jluisalegria/Access_Control/Firmware/Access_Control_IoT_Contest/figures/1import.png

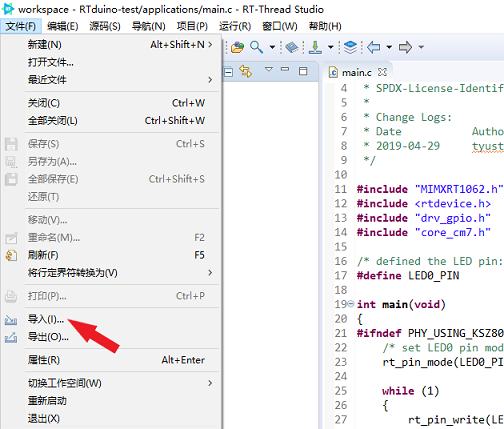
Firmware/Access_Control_IoT_Contest/figures/1import.png
