jluisalegria/Access_Control/Firmware/Access_Control_IoT_Contest/figures/2workspace.png

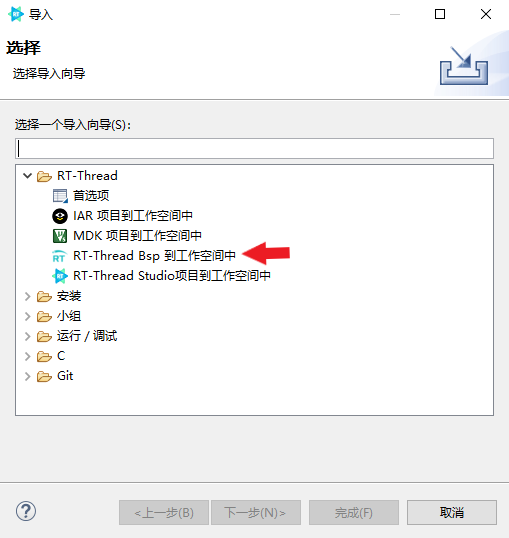
Firmware/Access_Control_IoT_Contest/figures/2workspace.png
