jluisalegria/Access_Control/Firmware/Access_Control_IoT_Contest/figures/3info.png

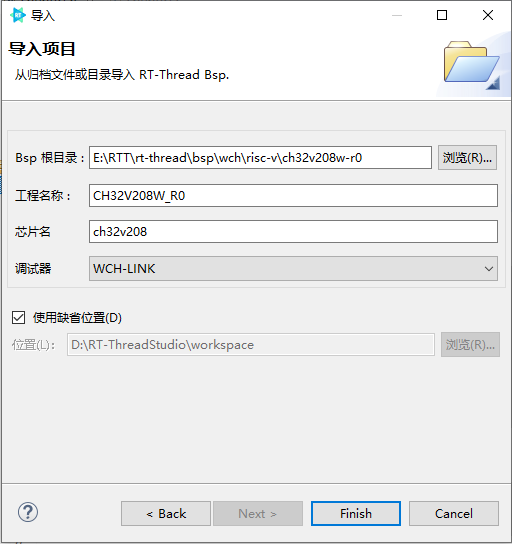
Firmware/Access_Control_IoT_Contest/figures/3info.png
