jluisalegria/Access_Control/Firmware/Access_Control_IoT_Contest/figures/6pkgs.png

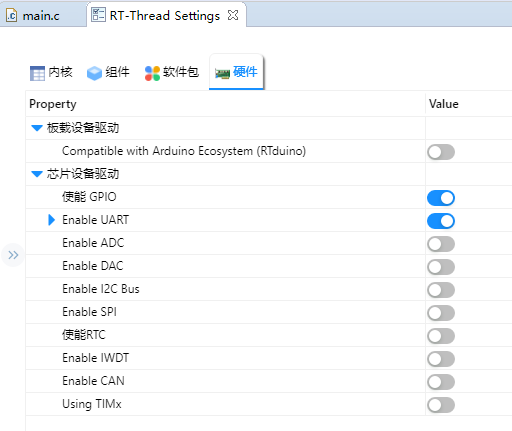
Firmware/Access_Control_IoT_Contest/figures/6pkgs.png
