jluisalegria/Access_Control/Firmware/Access_Control_IoT_Contest/figures/8setting.png

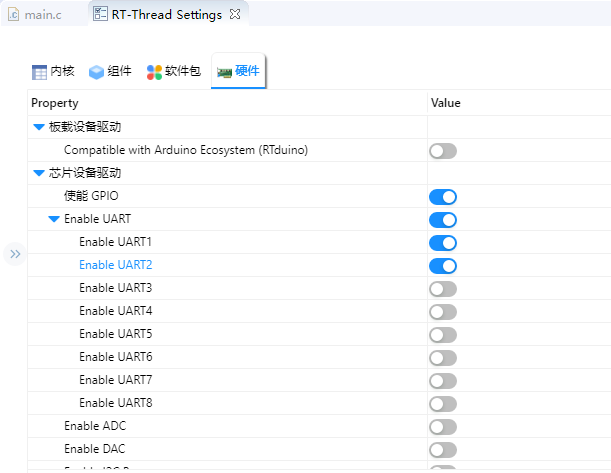
Firmware/Access_Control_IoT_Contest/figures/8setting.png
