jluisalegria/Access_Control/Firmware/Access_Control_IoT_Contest/figures/9AT.png

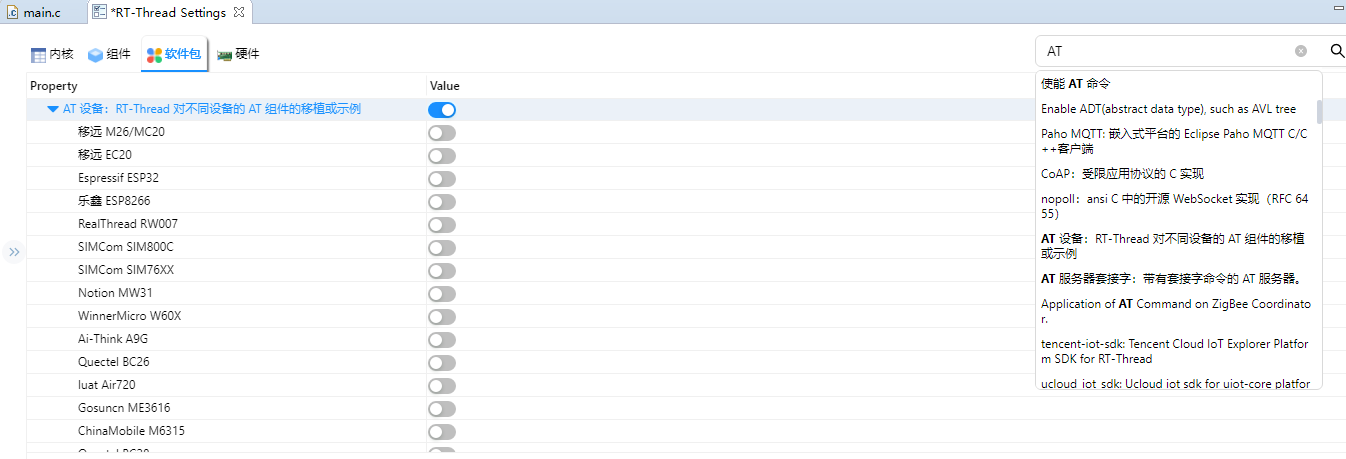
Firmware/Access_Control_IoT_Contest/figures/9AT.png
