jluisalegria/Access_Control/Firmware/Access_Control_IoT_Contest/figures/10wifinfo.png

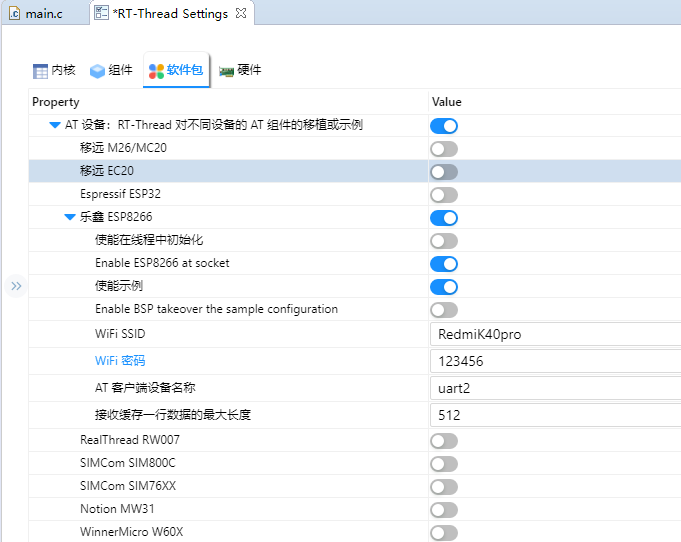
Firmware/Access_Control_IoT_Contest/figures/10wifinfo.png
