jluisalegria/Access_Control/Firmware/Access_Control_IoT_Contest/figures/16rtduino.png

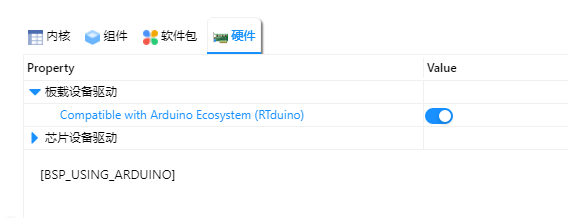
Firmware/Access_Control_IoT_Contest/figures/16rtduino.png
