jluisalegria/Access_Control/Firmware/Access_Control_IoT_Contest/figures/ch32v208.png

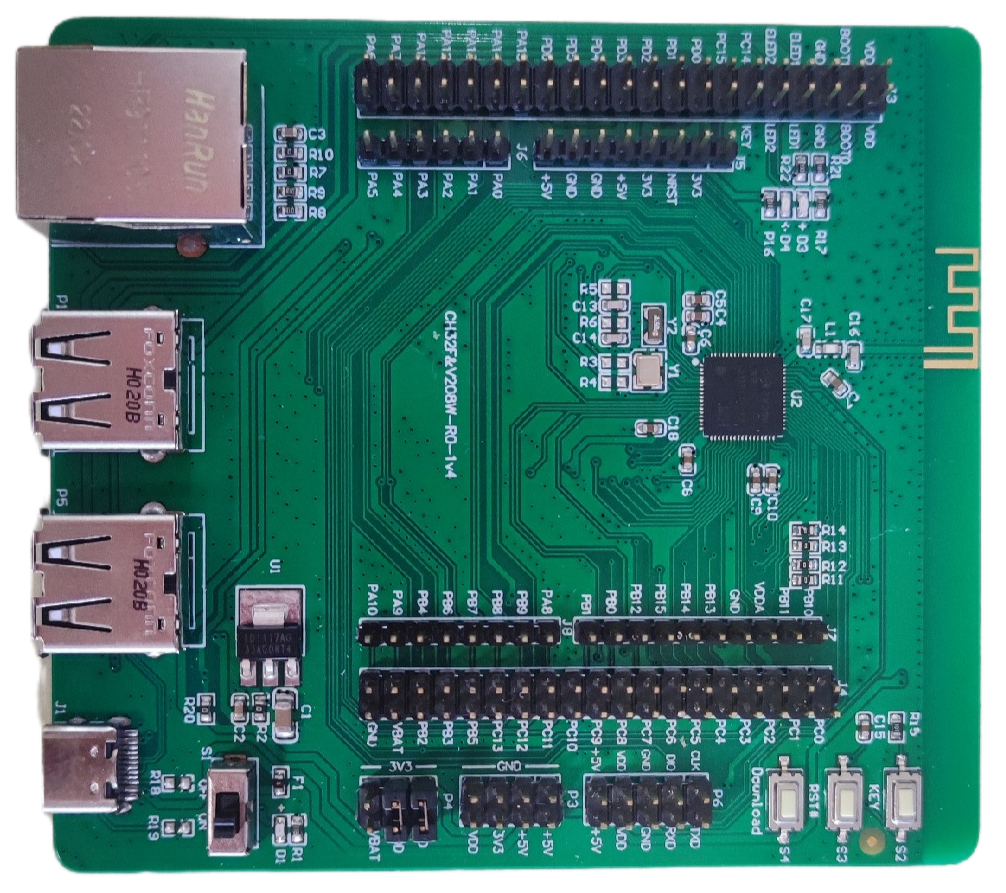
Firmware/Access_Control_IoT_Contest/figures/ch32v208.png
