jluisalegria/Access_Control/Firmware/Access_Control_IoT_Contest/figures/config.png

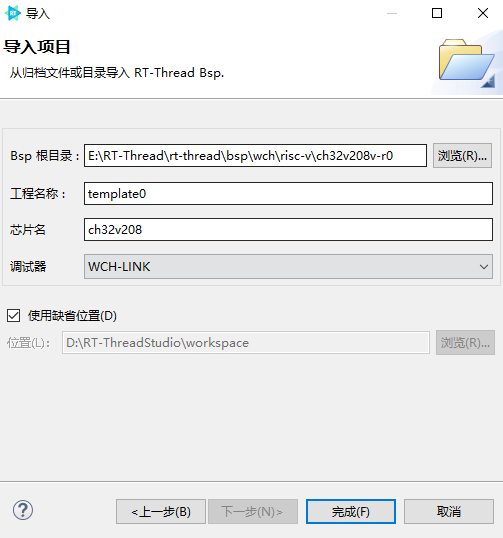
Firmware/Access_Control_IoT_Contest/figures/config.png
