jluisalegria/Access_Control/Firmware/Access_Control_IoT_Contest/figures/dist.png

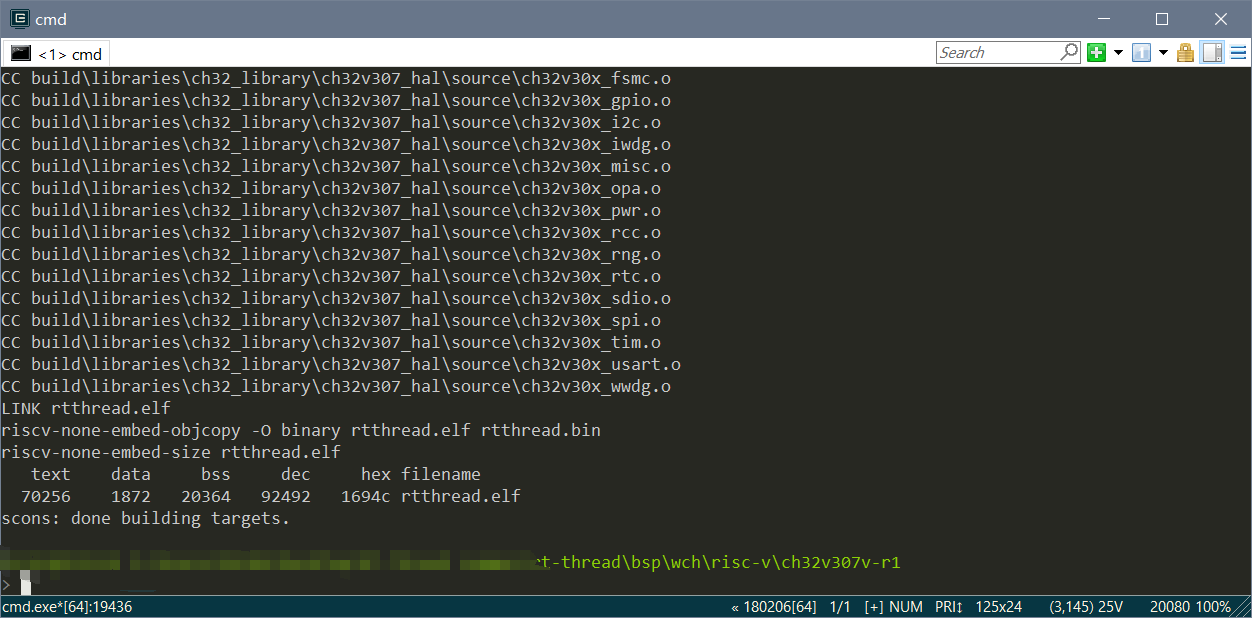
Firmware/Access_Control_IoT_Contest/figures/dist.png
