jluisalegria/Access_Control/Firmware/Access_Control_IoT_Contest/figures/end.png

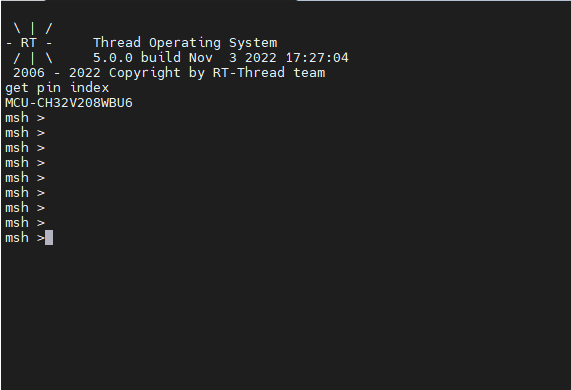
Firmware/Access_Control_IoT_Contest/figures/end.png
