jluisalegria/Access_Control/Firmware/Access_Control_IoT_Contest/figures/import.png

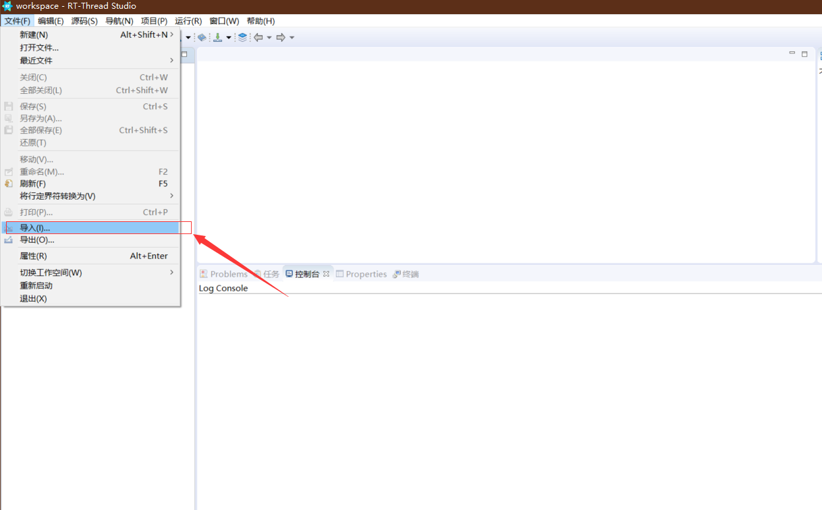
Firmware/Access_Control_IoT_Contest/figures/import.png
