jluisalegria/Access_Control/Firmware/Access_Control_IoT_Contest/figures/prefix.png

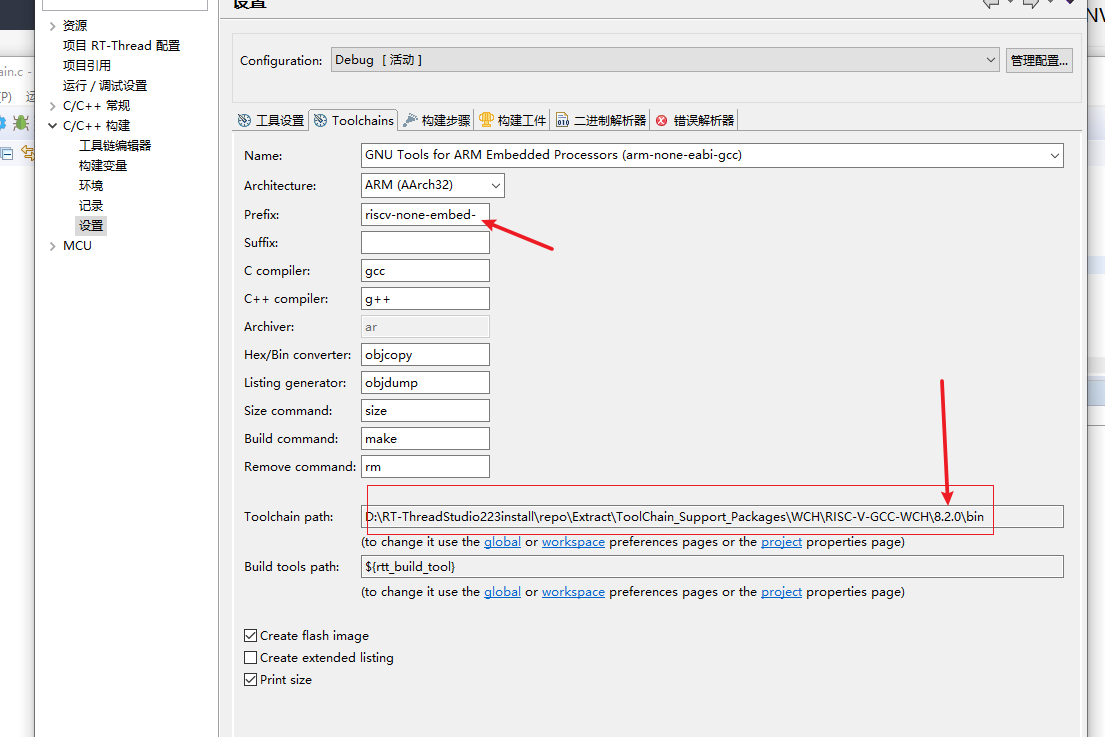
Firmware/Access_Control_IoT_Contest/figures/prefix.png
