jluisalegria/Access_Control/Firmware/Access_Control_IoT_Contest/figures/scons.png

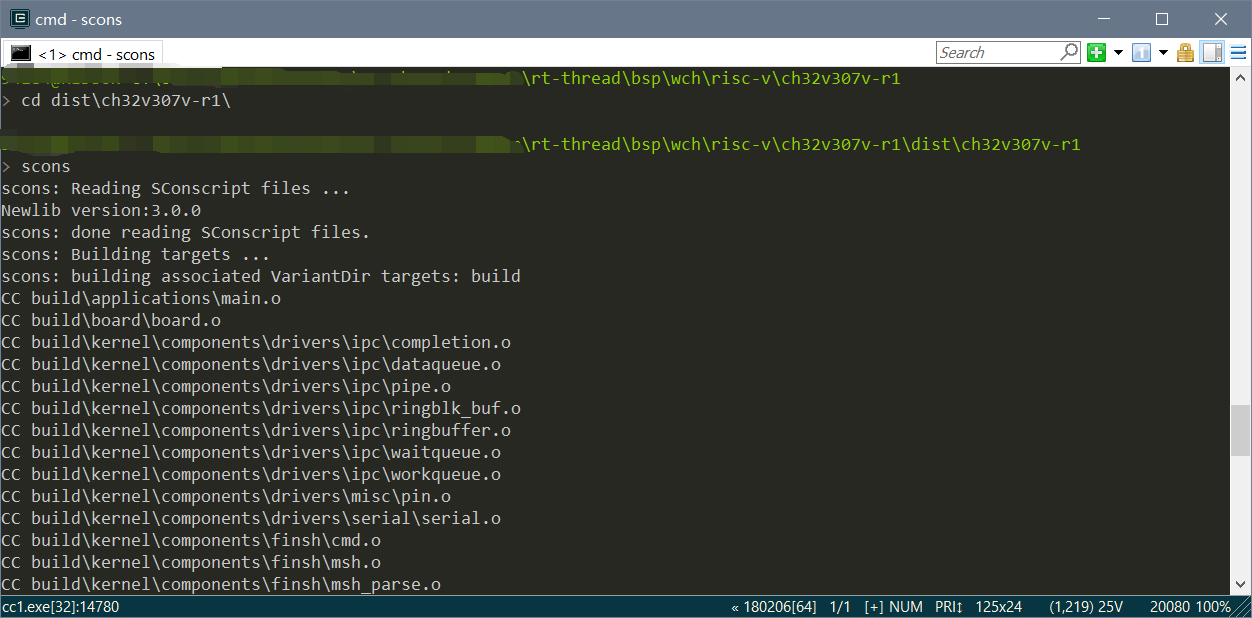
Firmware/Access_Control_IoT_Contest/figures/scons.png
