jluisalegria/Access_Control/Firmware/Access_Control_IoT_Contest/figures/success.png

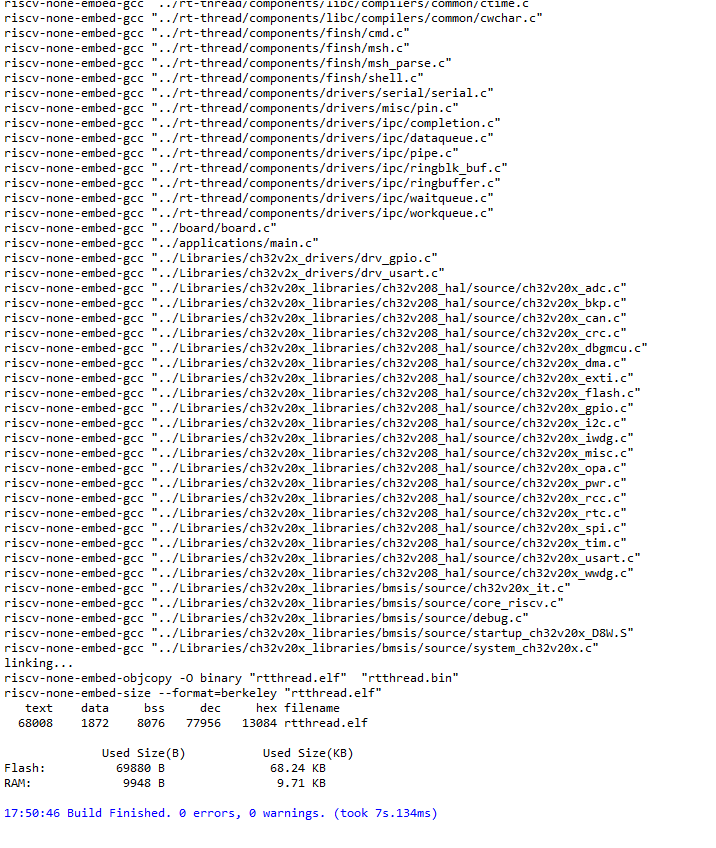
Firmware/Access_Control_IoT_Contest/figures/success.png
