jluisalegria/Access_Control/Firmware/Access_Control_IoT_Contest/figures/tool.png

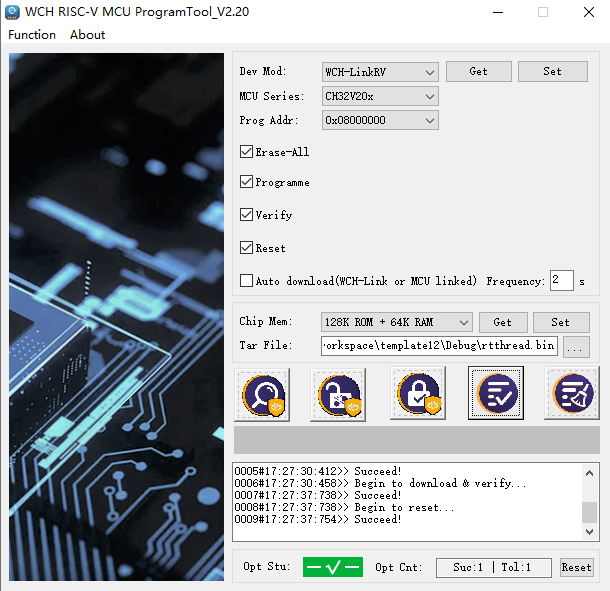
Firmware/Access_Control_IoT_Contest/figures/tool.png
