jluisalegria/Access_Control/Firmware/Access_Control_IoT_Contest/figures/toolchain.png

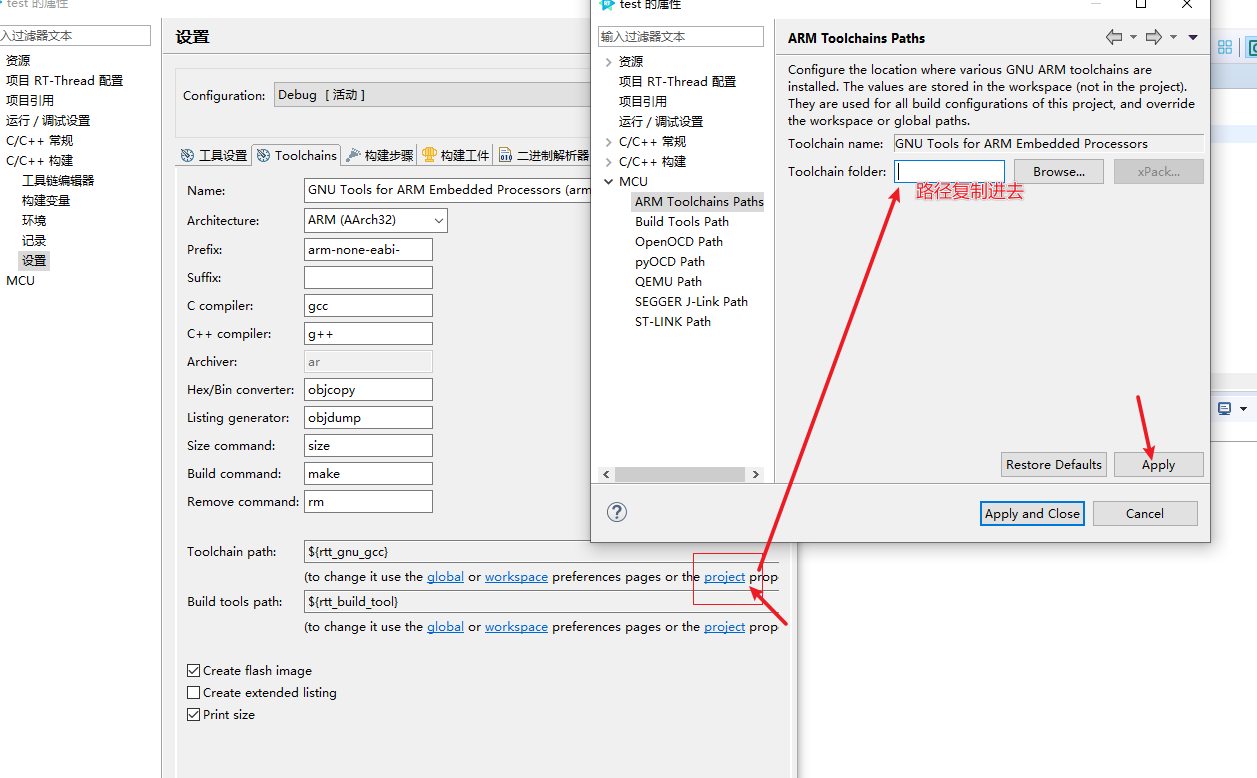
Firmware/Access_Control_IoT_Contest/figures/toolchain.png
