jluisalegria/Access_Control/Firmware/Access_Control_IoT_Contest/figures/toolset.png

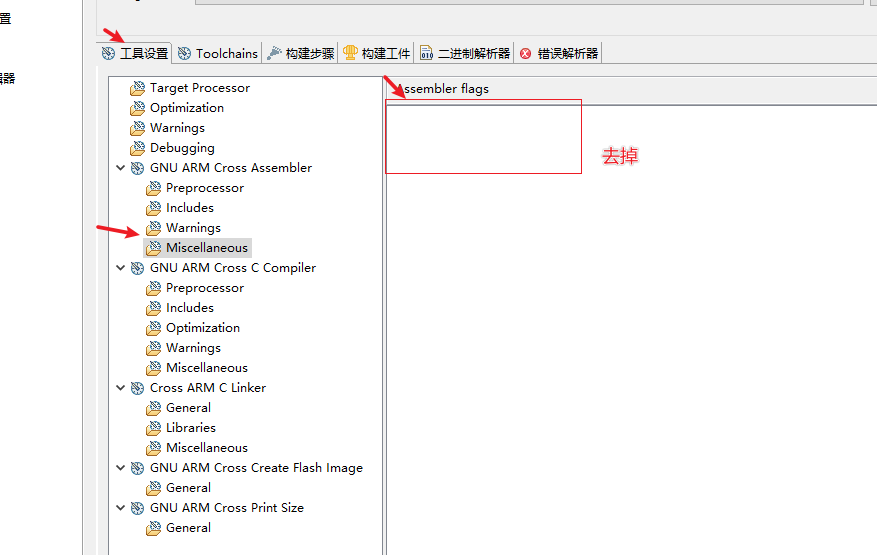
Firmware/Access_Control_IoT_Contest/figures/toolset.png
