jluisalegria/Access_Control/Firmware/Access_Control_IoT_Contest/figures/vscode-terminal.png

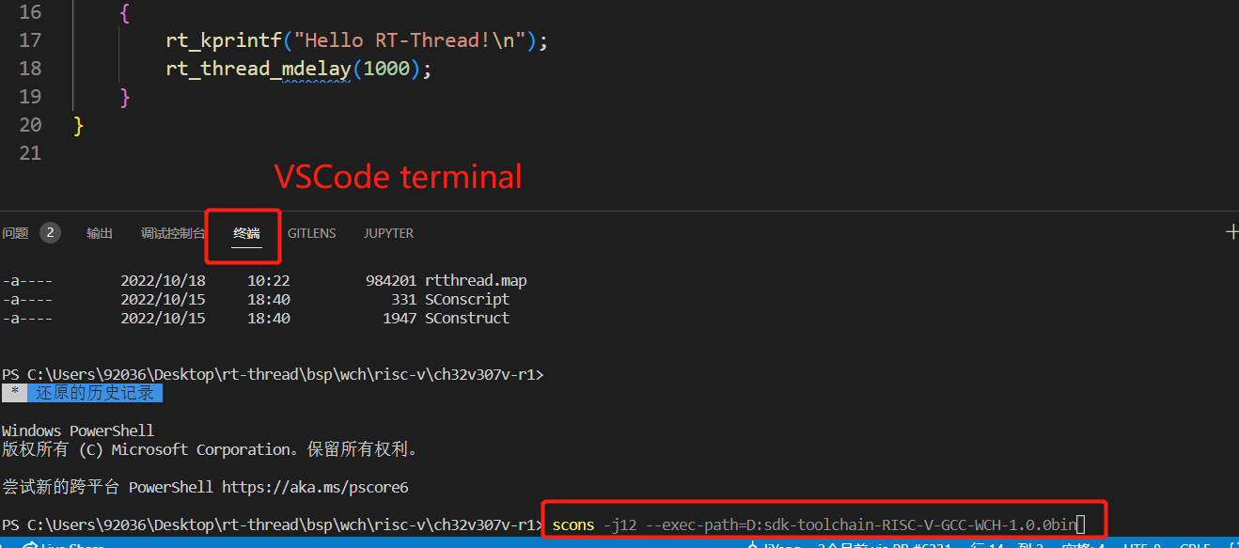
Firmware/Access_Control_IoT_Contest/figures/vscode-terminal.png
