jluisalegria/Access_Control/Firmware/Access_Control_IoT_Contest/figures/windows.png

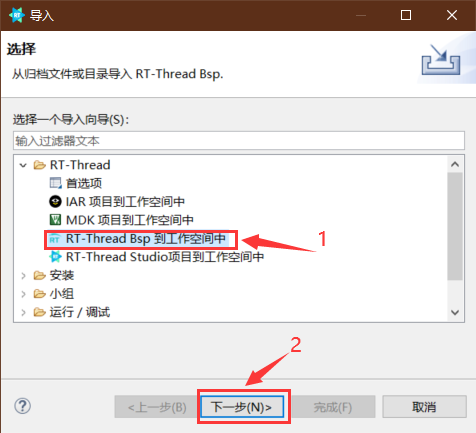
Firmware/Access_Control_IoT_Contest/figures/windows.png
