jluisalegria/Access_Control/Images/Relay.png

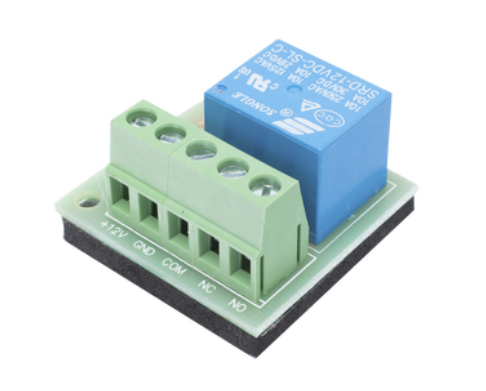
Images/Relay.png
