jluisalegria/Access_Control/Firmware/Access_Control_IoT_Contest/rt-thread/components/fal/docs/figures/fal-api-en.png

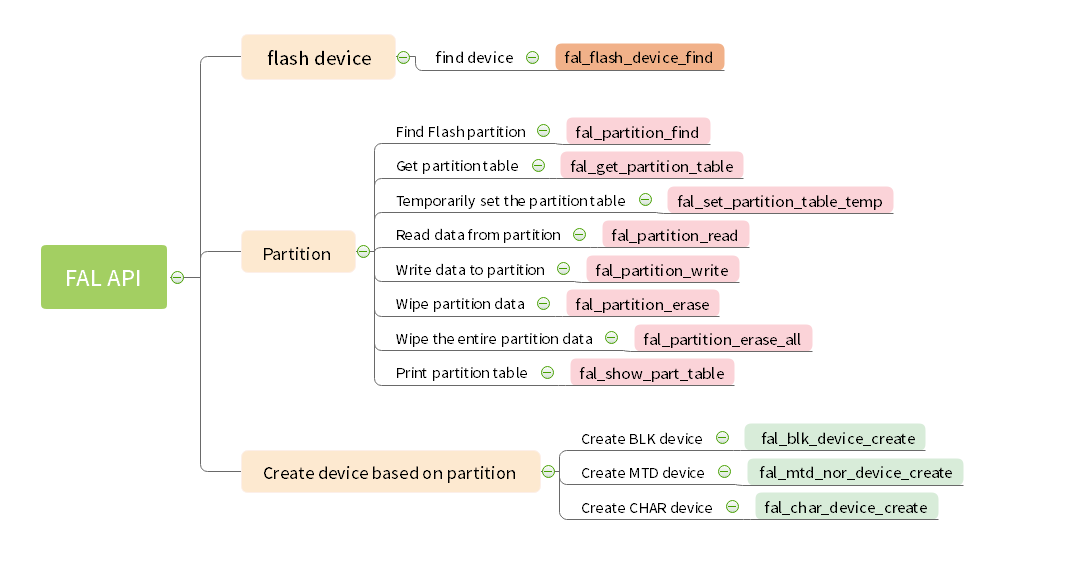
Firmware/Access_Control_IoT_Contest/rt-thread/components/fal/docs/figures/fal-api-en.png
