jluisalegria/Access_Control/Firmware/Access_Control_IoT_Contest/rt-thread/components/fal/docs/figures/fal_framework.png

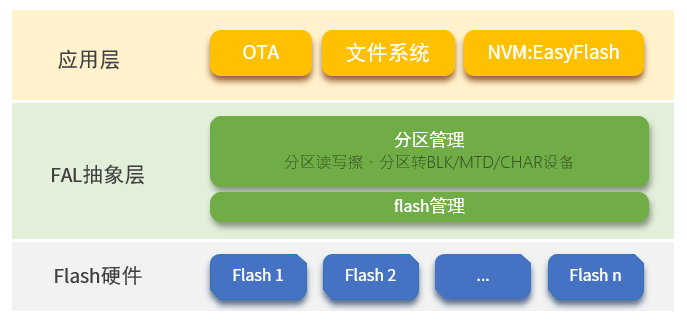
Firmware/Access_Control_IoT_Contest/rt-thread/components/fal/docs/figures/fal_framework.png
