jluisalegria/Access_Control/Firmware/Access_Control_IoT_Contest/figures/12kdebug.png

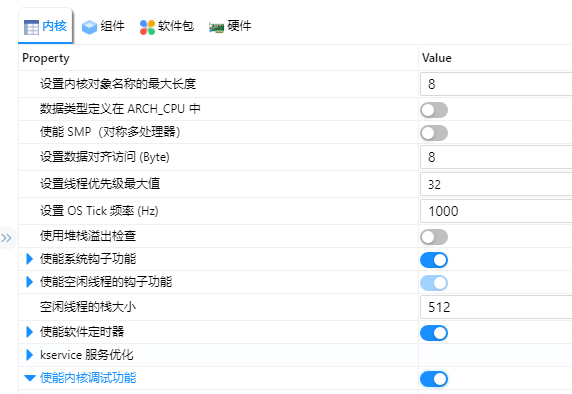
Firmware/Access_Control_IoT_Contest/figures/12kdebug.png
